aikos-home/roomkey/docs/fit-check-speaker.png

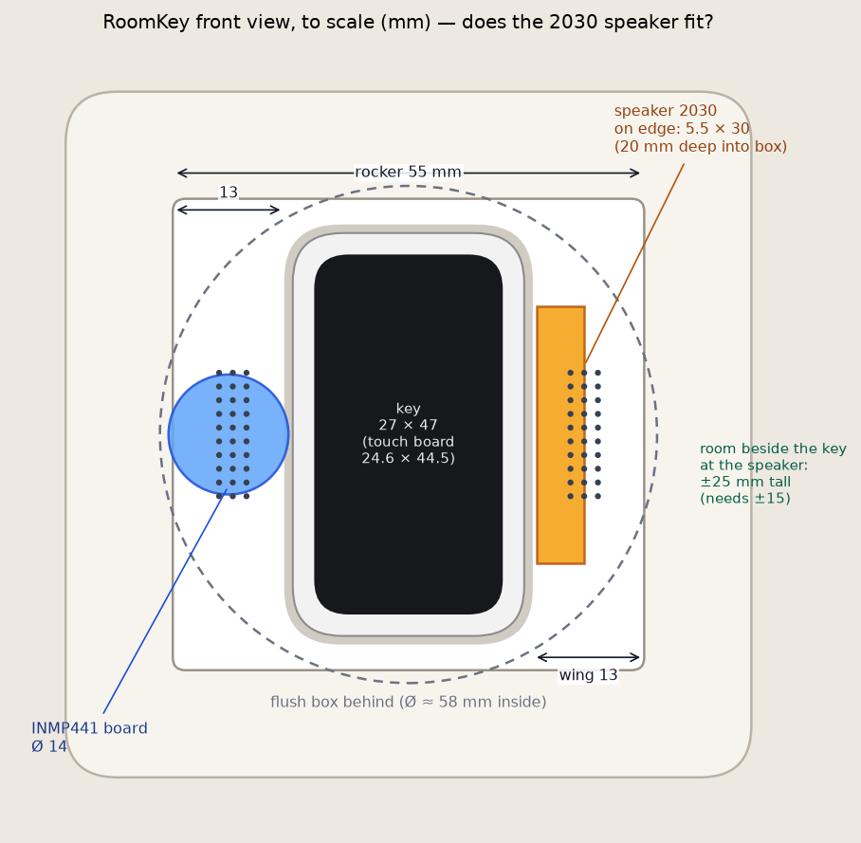
docs/fit-check-speaker.png
