aikos-home/roomkey/docs/north-star-v1.jpg

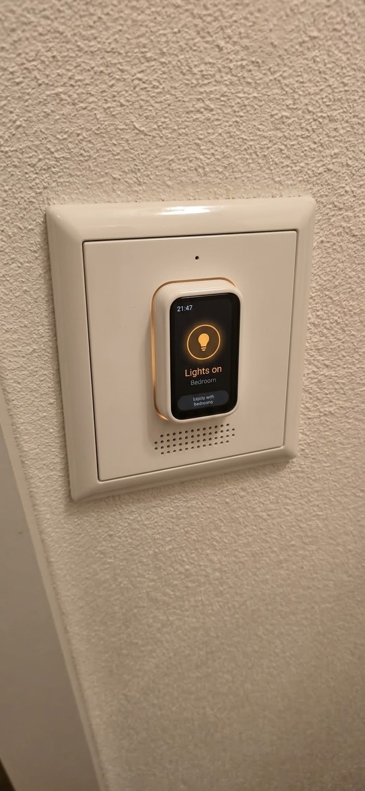
docs/north-star-v1.jpg
