aikos-home/roomkey/docs/screens/01_home_lights_off.png

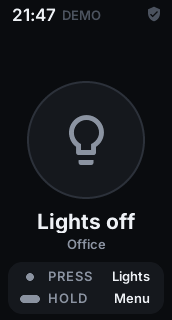
docs/screens/01_home_lights_off.png
