aikos-home/roomkey/docs/screens/02_home_hold_for_menu.png

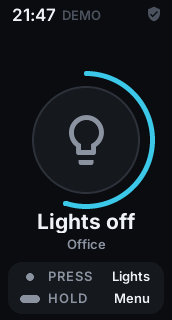
docs/screens/02_home_hold_for_menu.png
