aikos-home/roomkey/docs/screens/03_menu.png

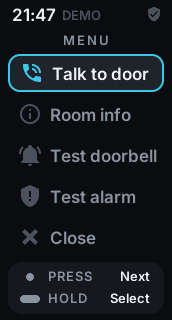
docs/screens/03_menu.png
