aikos-home/roomkey/docs/screens/05_doorbell_ringing.png

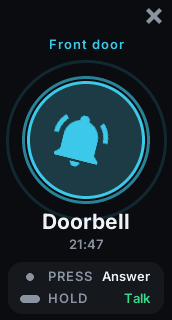
docs/screens/05_doorbell_ringing.png
