aikos-home/roomkey/docs/screens/06_call_talking_hold.png

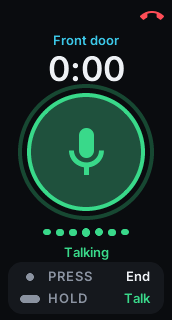
docs/screens/06_call_talking_hold.png
