aikos-home/roomkey/docs/screens/07_call_listening.png

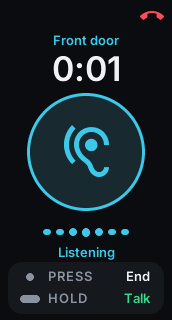
docs/screens/07_call_listening.png
