aikos-home/roomkey/docs/screens/09_home_armed_night.png

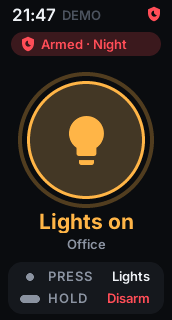
docs/screens/09_home_armed_night.png
