aikos-home/roomkey/docs/screens/10_home_hold_to_disarm.png

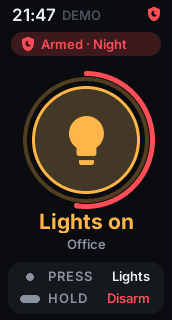
docs/screens/10_home_hold_to_disarm.png
