aikos-home/roomkey/docs/screens/11_disarming.png

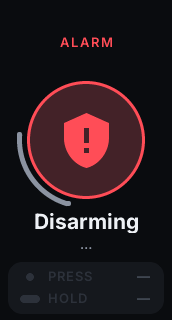
docs/screens/11_disarming.png
