aikos-home/roomkey/docs/screens/12_disarmed_flash.png

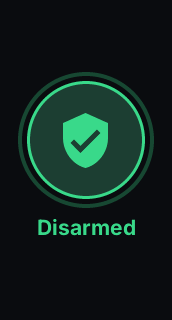
docs/screens/12_disarmed_flash.png
