aikos-home/roomkey/docs/screens/13_alarm_entry_delay.png

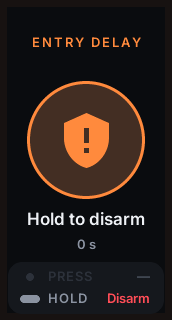
docs/screens/13_alarm_entry_delay.png
