aikos-home/roomkey/docs/screens/14_alarm_triggered.png

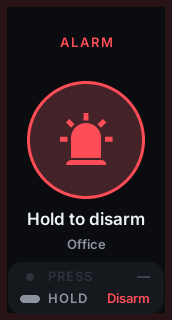
docs/screens/14_alarm_triggered.png
