aikos-home/roomkey/docs/screens/15_room_info.png

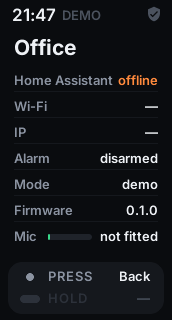
docs/screens/15_room_info.png
