aikos-home/roomkey/docs/screens/16_offline_toast.png

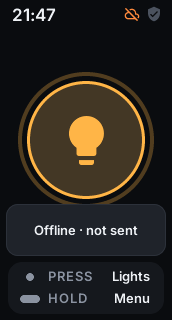
docs/screens/16_offline_toast.png
