aikos-home/roomkey/docs/screens/e2e_01_lights_on_via_ha.png

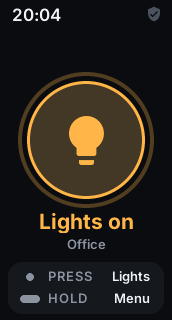
docs/screens/e2e_01_lights_on_via_ha.png
