aikos-home/roomkey/docs/screens/e2e_03_ring_from_ha_entity.png

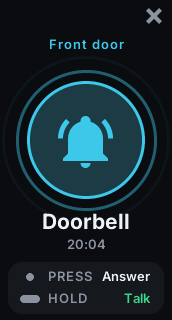
docs/screens/e2e_03_ring_from_ha_entity.png
