aikos-home/roomkey/docs/screens/e2e_04_entry_delay_from_ha.png

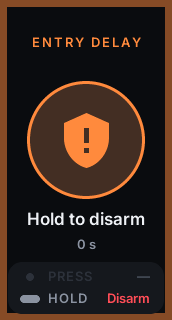
docs/screens/e2e_04_entry_delay_from_ha.png
