aikos-home/roomkey/hardware/drawings/insert-L_layers.png

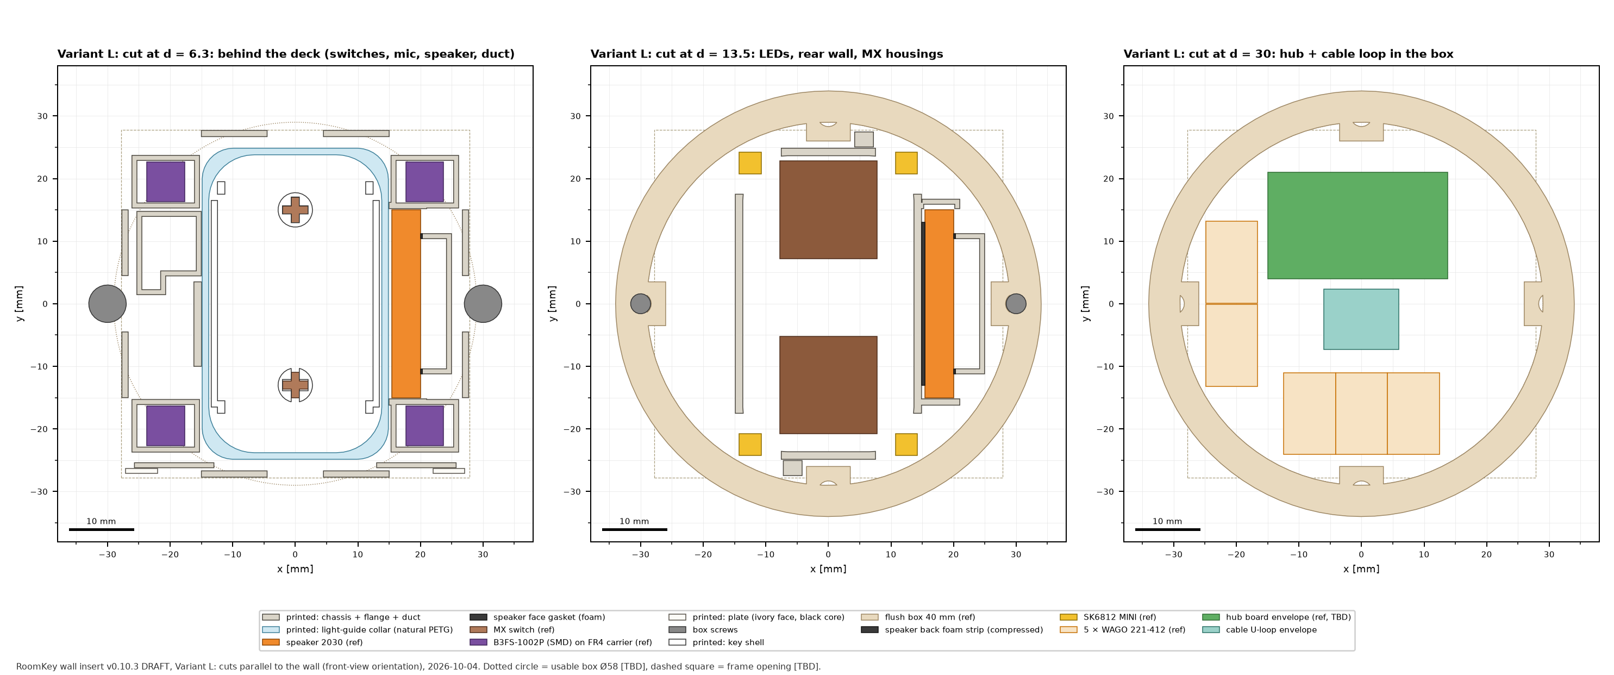
hardware/drawings/insert-L_layers.png
