aikos-home/roomkey/hardware/models/kit_chassis_3_rear_print.stl

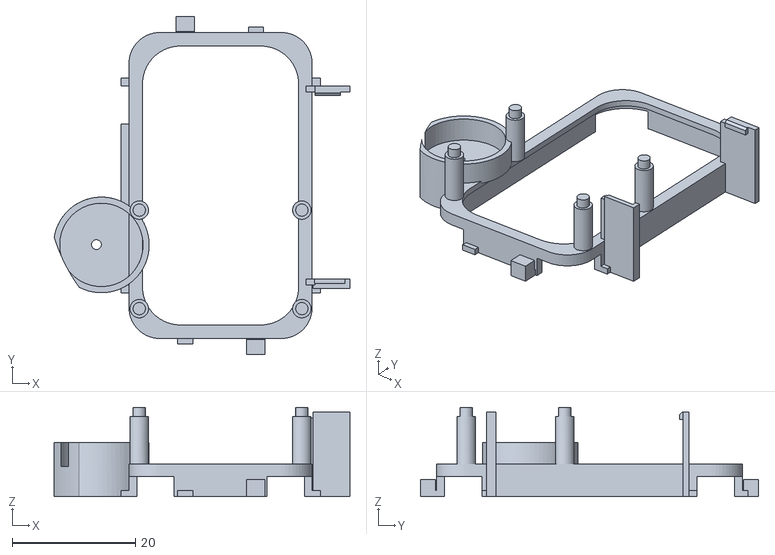
[picture p46: CAD file, 2026-10-08]
hardware/models/kit_chassis_3_rear_print.stl
48.0 x 54.9 x 14.5
