aikos-home/roomkey/hardware/models/chassis_S_2_flange.step

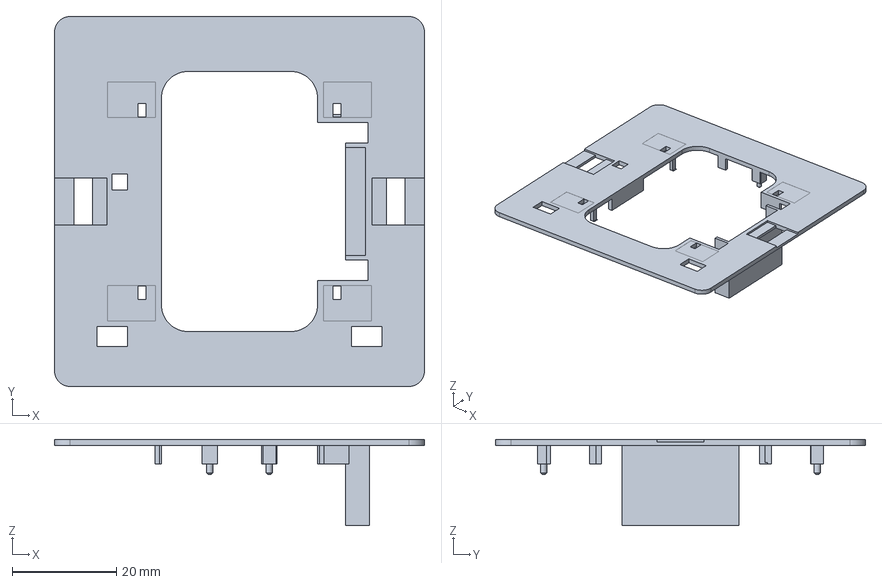
[picture p47: CAD file, 2026-10-08]
hardware/models/chassis_S_2_flange.step
71.0 x 71.0 x 16.5 mm
