aikos-home/roomkey/hardware/models/kit_chassis_2_flange.step

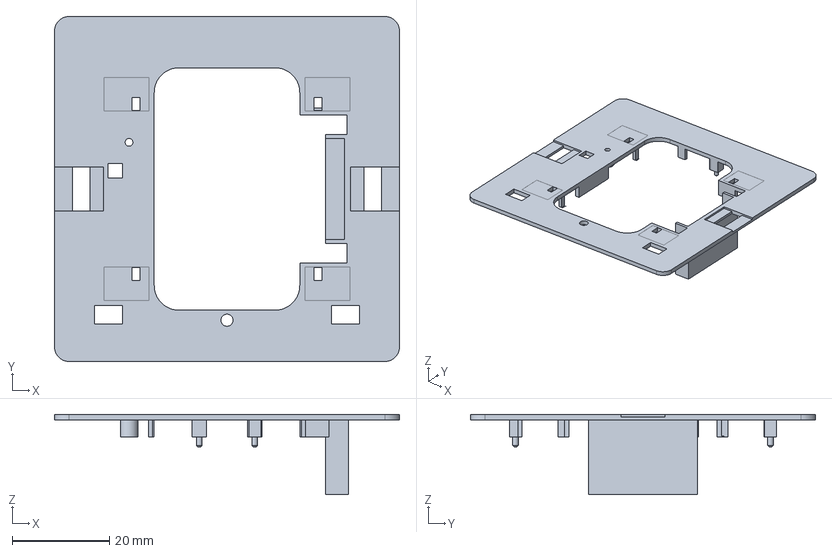
[picture p48: CAD file, 2026-10-08]
hardware/models/kit_chassis_2_flange.step
71.0 x 71.0 x 16.5 mm
