aikos-home/roomkey/hardware/models/chassis_L.step

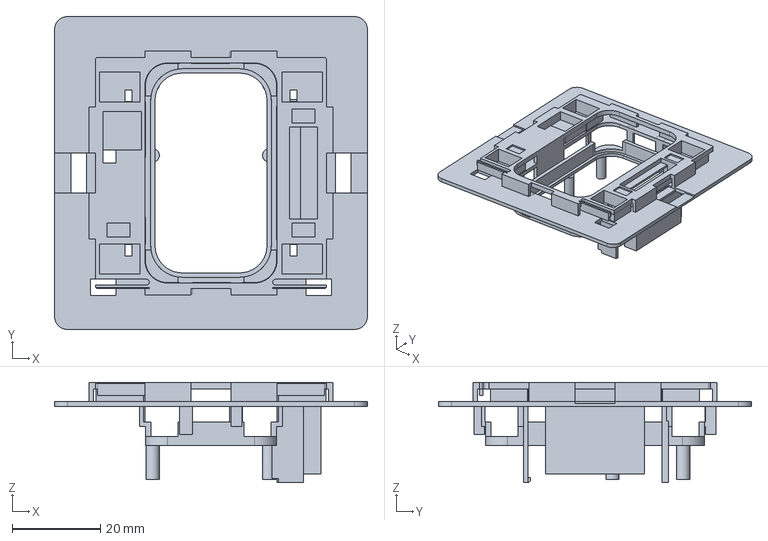
[picture p49: CAD file, 2026-10-08]
hardware/models/chassis_L.step
71.0 x 71.0 x 22.7 mm
