aikos-home/roomkey/hardware/models/switch_plate_print.stl

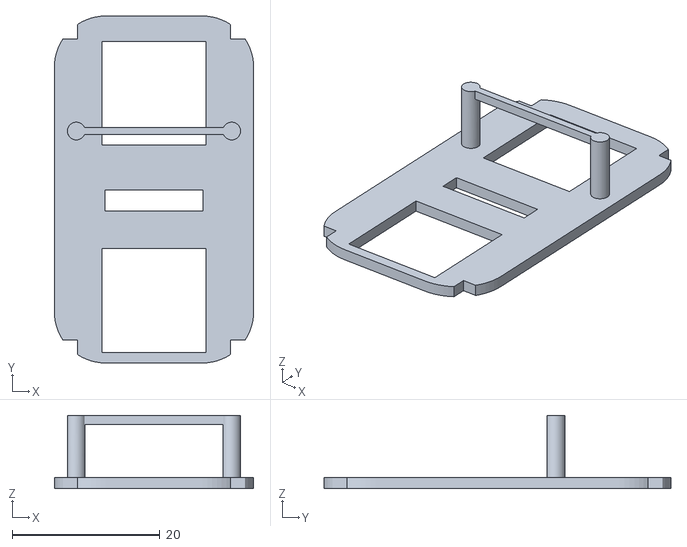
[picture p50: CAD file, 2026-10-08]
hardware/models/switch_plate_print.stl
27.0 x 46.9 x 9.90
