aikos-home/roomkey/hardware/models/kit-v0.10.3_ansicht.FCStd

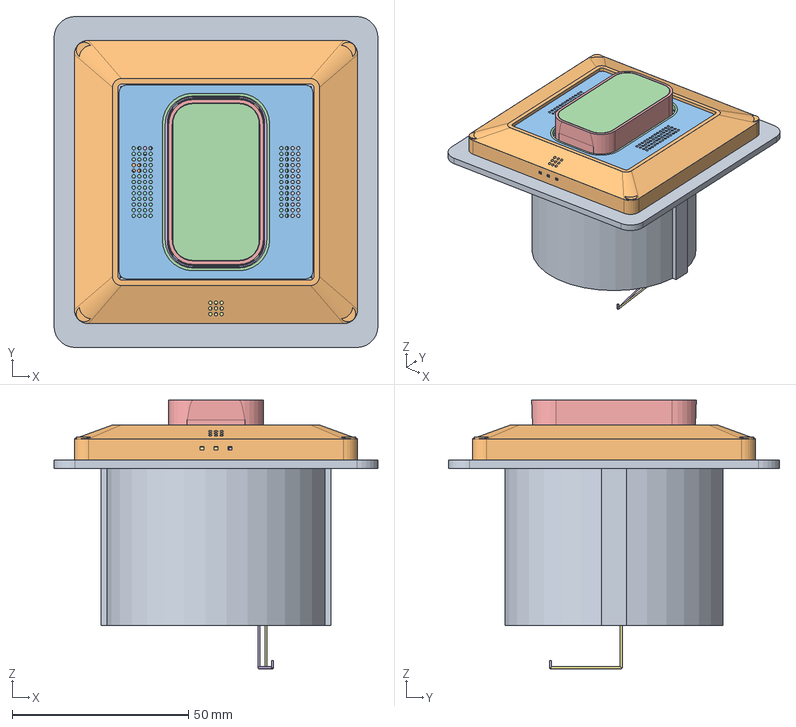
[picture p51: CAD file, 2026-10-08]
hardware/models/kit-v0.10.3_ansicht.FCStd
92.0 x 94.0 x 76.3 mm
Uebungsdose
Rahmen_JungAS500
Platte
Platte_Leuchtrand
Tastenschale_starr
Leuchtring
Schalterplatte
Chassis_1_vorne
Chassis_2_Flansch
Chassis_3_hinten
Technik_Traeger
Touch_Board
MX_oben
MX_unten
Lautsprecher
Radar_LD2410C
Radar_Stiftleiste
Radar_Chip_vorne
Radar_Randbauteile_vorne
Radar_Stiftstummel_vorne
Verstaerker_MAX98357A
Mikrofon_INMP441
Feuchtesensor_SHT31D_im_Rahmen
Kabelbogen_Taste
LED_1
LED_2
LED_3
LED_4
Schraube_links
Schraube_rechts
Draht 01 · 5 V → board · rot
Draht 02 · GND → board · schwarz
Draht 03 · KEY1 (Taste oben) · weiß
Draht 04 · KEY2 (Taste unten) · grau
Draht 05 · GND Taste oben · schwarz
Draht 06 · GND Taste unten (Brücke) · schwarz
Draht 07 · Radar TX → ESP RX · gelb
Draht 08 · ESP TX → Radar RX · grün
Draht 09 · 5 V Radar · rot
Draht 10 · GND Radar · schwarz
Draht 11 · I²S BCLK (Verstärker) · blau
Draht 12 · I²S WS (Verstärker) · violett
Draht 13 · I²S Daten → Verstärker · braun
Draht 14 · 5 V Verstärker · rot
Draht 15 · GND Verstärker · schwarz
Draht 16 · Lautsprecher + · rot
Draht 17 · Lautsprecher − · schwarz
Draht 18 · I²S BCLK (Mikrofon, vom Verstärker weiter) · blau
Draht 19 · I²S WS (Mikrofon, vom Verstärker weiter) · violett
Draht 20 · I²S Daten ← Mikrofon · rosa
Draht 21 · 3,3 V Mikrofon · orange
Draht 22 · L/R auf GND (linker Kanal) · schwarz
Draht 23 · GND Mikrofon · schwarz
Draht 24 · Labornetzteil +5,0 V · rot
Draht 25 · Labornetzteil GND · schwarz
Draht 26 · LED-Daten → LED unten rechts · gelb-grün
Draht 27 · LED-Daten → oben rechts · gelb-grün
Draht 28 · LED-Daten → oben links · gelb-grün
Draht 29 · LED-Daten → unten links · gelb-grün
Draht 30 · 5 V LED unten rechts · rot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
