aikos-home/roomkey/hardware/models/kit_chassis_1_front_print.stl

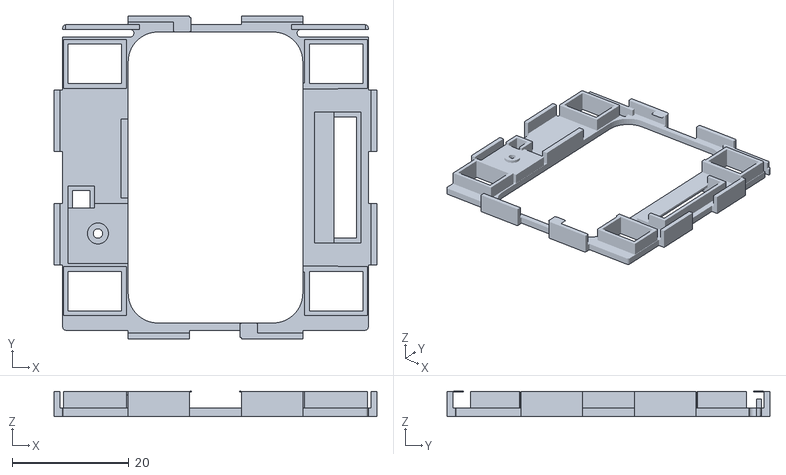
[picture p52: CAD file, 2026-10-08]
hardware/models/kit_chassis_1_front_print.stl
55.4 x 55.4 x 4.30
