aikos-home/roomkey/hardware/models/practice_frame_1x.step

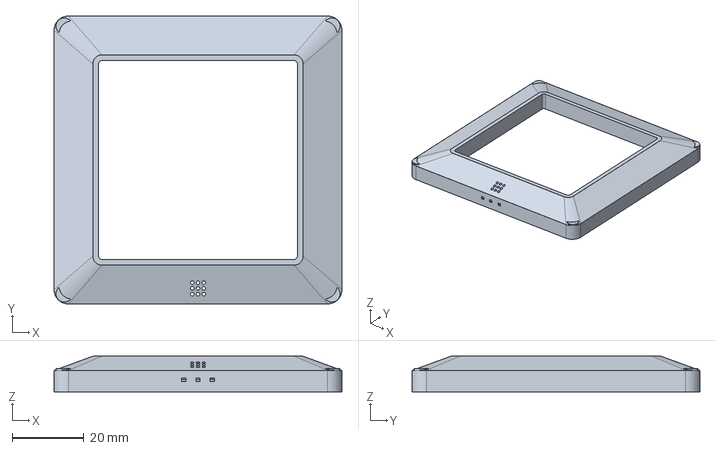
[picture p53: CAD file, 2026-10-06]
hardware/models/practice_frame_1x.step
80.5 x 80.5 x 10.0 mm
