aikos-home/roomkey/hardware/models/plate_L.step

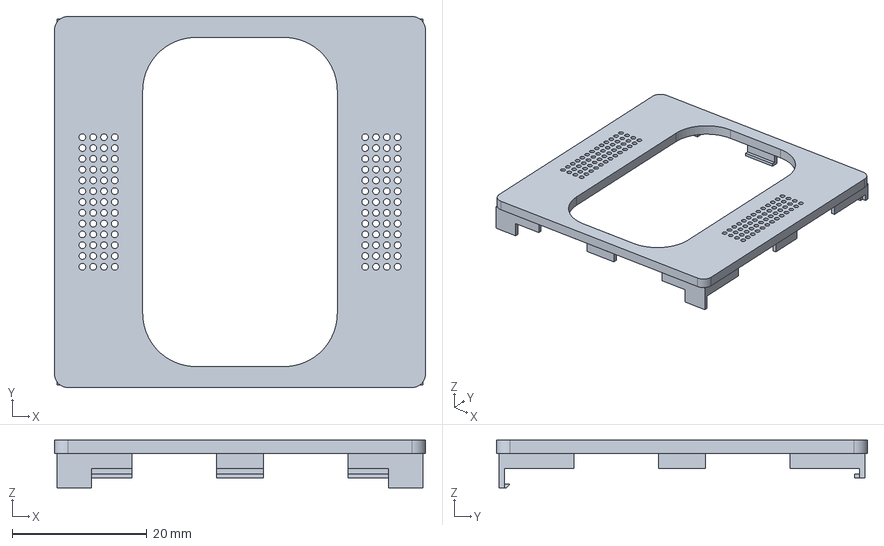
[picture p54: CAD file, 2026-10-04]
hardware/models/plate_L.step
55.0 x 55.0 x 7.10 mm
