aikos-home/roomkey/hardware/models/insert-L_wall-reference.step

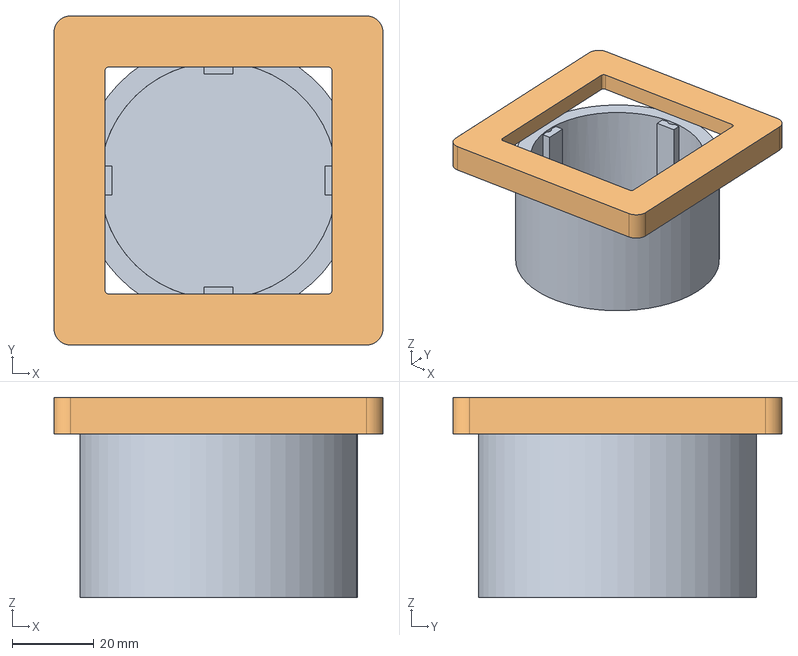
[picture p55: CAD file, 2026-10-04]
hardware/models/insert-L_wall-reference.step
80.5 x 80.5 x 49.0 mm
