aikos-home/roomkey/hardware/models/practice_box_print.stl

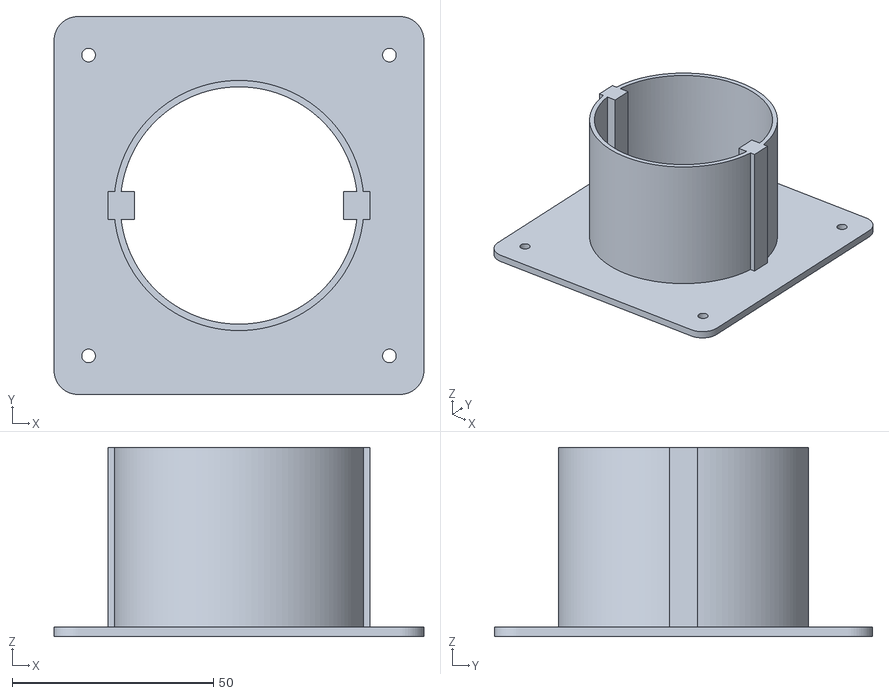
[picture p56: CAD file, 2026-10-04]
hardware/models/practice_box_print.stl
92.0 x 94.0 x 47.0
