aikos-home/roomkey/hardware/models/coupon-v1.step

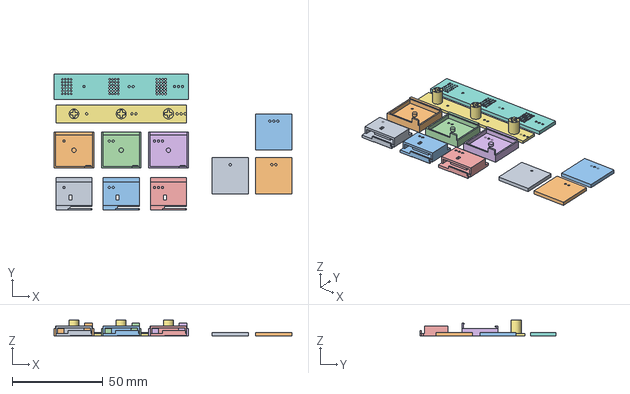
[picture p57: CAD file, 2026-10-01]
hardware/models/coupon-v1.step
131.0 x 75.0 x 8.80 mm
