aikos-home/roomkey/hardware/models/plate_S_body_print.stl

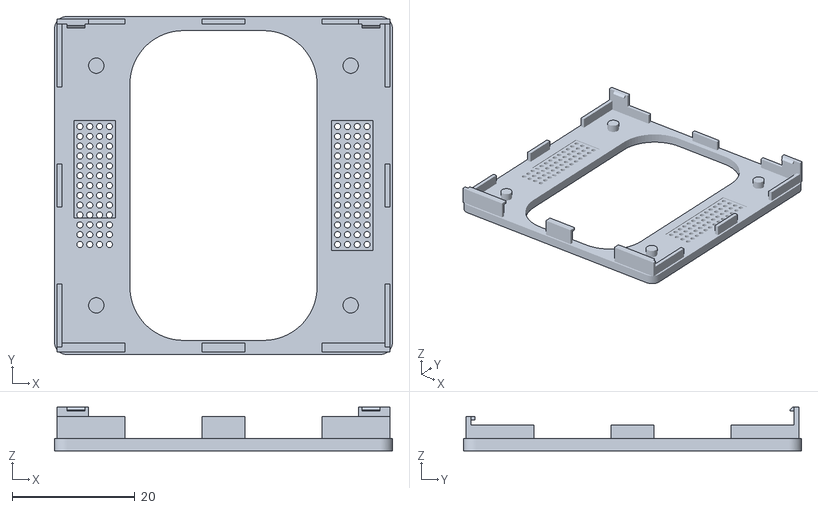
[picture p58: CAD file, 2026-10-01]
hardware/models/plate_S_body_print.stl
55.0 x 55.0 x 7.10
