aikos-home/roomkey/hardware/models/plate_L_glowrim_print.stl

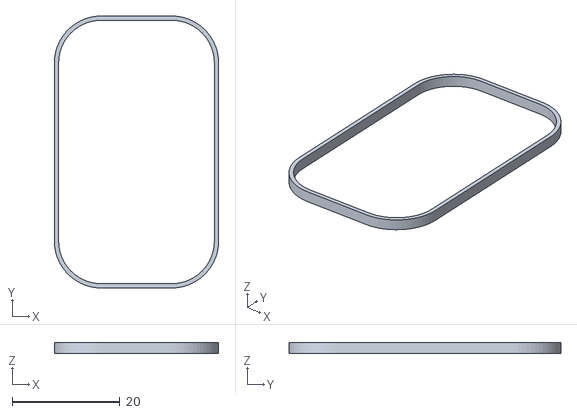
[picture p59: CAD file, 2026-10-01]
hardware/models/plate_L_glowrim_print.stl
30.5 x 50.4 x 2.00
