aikos-home/roomkey/esphome/src/roomkey_audio.h

#pragma once
// ─────────────────────────────────────────────────────────────────────────────
// RoomKey audio link (WIP) — half-duplex intercom media over UDP.
//
//   Format   RTP (RFC 3550) · L16 big-endian (RFC 3551) · 16 kHz · mono ·
//            dynamic payload type 96 · 20 ms / 320 samples per packet
//   Port     local UDP 5004 (configurable)
//   Peer     set explicitly (action set_intercom_peer) or *latched*: the first
//            host that streams to us becomes the peer (symmetric RTP) — so the
//            door station only needs to know the key's IP.
//
//   Tap      optional second destination (the local transcriber): every packet we SEND
//            also goes there, so what the room says can be transcribed. Only our own
//            microphone, only while we transmit (push-to-talk). Unset = off.
//
// Signalling (who talks when) is NOT here: it goes through Home Assistant
// (events answer / talk_start / talk_stop / hangup, action call_state).
// Threading: push_*() is called from the microphone task and only writes a
// lock-free SPSC ring; loop() runs in the main loop and owns the socket.
// ─────────────────────────────────────────────────────────────────────────────

#include <atomic>
#include <cmath>
#include <cstdint>
#include <cstdlib>
#include <cstring>
#include <functional>
#include <string>

#include "esphome/core/hal.h"
#include "roomkey_dsp.h"
#include "esphome/core/log.h"

#ifdef USE_HOST
#include <arpa/inet.h>
#include <fcntl.h>
#include <netdb.h>
#include <netinet/in.h>
#include <sys/socket.h>
#include <unistd.h>
#else
#include "lwip/netdb.h"
#include "lwip/sockets.h"
#endif

namespace roomkey {

class AudioLink {
 public:
  static constexpr int RATE = 16000;
  static constexpr int FRAME = 320;  // 20 ms
  static constexpr uint8_t PT_L16 = 96;

  bool begin(uint16_t port) {
    if (sock_ >= 0) return true;
    sock_ = ::socket(AF_INET, SOCK_DGRAM, IPPROTO_UDP);
    if (sock_ < 0) { ESP_LOGE(TAG, "socket() failed"); return false; }
    sockaddr_in a{};
    a.sin_family = AF_INET;
    a.sin_port = htons(port);
    a.sin_addr.s_addr = htonl(INADDR_ANY);
    if (::bind(sock_, (sockaddr *) &a, sizeof(a)) < 0) {
      ESP_LOGE(TAG, "bind(%u) failed", port);
      ::close(sock_);
      sock_ = -1;
      return false;
    }
    int fl = ::fcntl(sock_, F_GETFL, 0);
    ::fcntl(sock_, F_SETFL, fl | O_NONBLOCK);
    ssrc_ = 0x524B0000u ^ (uint32_t) esphome::millis();  // "RK" + noise
    port_ = port;
    ESP_LOGI(TAG, "RTP/L16 16 kHz listening on UDP %u", port);
    return true;
  }

  static bool resolve(const std::string &host, uint16_t port, sockaddr_in &a) {
    a = sockaddr_in{};
    a.sin_family = AF_INET;
    a.sin_port = htons(port);
    if (::inet_aton(host.c_str(), &a.sin_addr) != 0) return true;
    addrinfo hints{}, *res = nullptr;
    hints.ai_family = AF_INET;
    hints.ai_socktype = SOCK_DGRAM;
    if (::getaddrinfo(host.c_str(), nullptr, &hints, &res) != 0 || res == nullptr) {
      ESP_LOGW(TAG, "cannot resolve %s", host.c_str());
      return false;
    }
    a.sin_addr = ((sockaddr_in *) res->ai_addr)->sin_addr;
    ::freeaddrinfo(res);
    return true;
  }

  void set_peer(const std::string &host, uint16_t port) {
    sockaddr_in a;
    if (!resolve(host, port, a)) return;
    peer_ = a;
    has_peer_ = true;
    latched_ = false;
    clear_after_drain_ = false;
    keepalive_();  // resolve the peer's MAC now, not with the first words
    ESP_LOGI(TAG, "peer set to %s:%u", ::inet_ntoa(a.sin_addr), port);
  }
  void clear_peer() {
    if (closing_) { clear_after_drain_ = true; return; }  // still sending the last buffered words
    has_peer_ = false;
    latched_ = false;
  }
  // "host:port" of the transcriber, "" = off.
  void set_tap(const std::string &hp) {
    has_tap_ = false;
    size_t p = hp.rfind(':');
    if (p == std::string::npos || p == 0) {
      if (!hp.empty()) ESP_LOGW(TAG, "transcriber address must be host:port");
      return;
    }
    if (resolve(hp.substr(0, p), (uint16_t) atoi(hp.c_str() + p + 1), tap_)) {
      has_tap_ = true;
      keepalive_();
      ESP_LOGI(TAG, "transcriber tap %s", hp.c_str());
    }
  }
  // End of a call: forget a latched peer so the next caller can latch.
  void end_session() {
    set_tx(false);
    if (latched_) clear_peer();
  }
  // Accept incoming audio only while a call is active. Outside a call every packet is
  // dropped unheard and nobody can latch — otherwise any device on the LAN could play
  // sound in a bedroom.
  void set_accept(bool on) {
    if (accept_ && !on && latched_) clear_peer();
    accept_ = on;
  }
  // Where received audio goes (the speaker). Unset = received audio is only metered.
  std::function<void(const int16_t *, size_t)> sink;

  // Transmit gate (push-to-talk). On: a fresh start (stale samples are dropped). Off: take no
  // new samples, but still send what is buffered (≤ 256 ms), so the last word is not cut off.
  // to_peer = false: only the transcriber tap gets it (the test recording after a ring must never reach
  // the door; room audio goes to the door only while the key is held).
  void set_tx(bool on, bool to_peer = true) {
    if (on) {
      tail_.store(head_.load(std::memory_order_acquire));  // consumer-side drop of stale samples
      closing_ = false;
      to_peer_ = to_peer;
      tx_ = true;
    } else if (tx_) {
      closing_ = true;
    }
  }
  bool tx() const { return tx_ && !closing_; }

  // End-of-speech detection for timed recordings (mic task, once per mic block): speech is
  // VOICE_DB above the room's noise floor = the quietest block of the last ~1.5 s (speech has
  // gaps between words; steady noise does not). Muted start-up blocks don't count.
  void note_level(float db) { mic_gate.note(db, esphome::millis()); }
  float noise_floor_db() const { return mic_gate.floor_db(); }
  // Has anyone spoken since t0 (millis)?
  bool voiced_since(uint32_t t0) const { return mic_gate.voiced_since(t0); }
  uint32_t quiet_ms() const { return mic_gate.quiet_ms(esphome::millis()); }
  VoiceGate mic_gate;   // this key's mic (mic task)
  VoiceGate rx_gate;    // what comes in from the door (main loop): speech, not packets, ends a call (R17.8)

  // Producer side (microphone task): Q31 samples, optional gain.
  void push_q31(const int32_t *s, size_t n, float gain = 4.0f) {
    if (!tx_ || closing_) return;
    for (size_t i = 0; i < n; i++) {
      float v = (s[i] >> 16) * gain;
      put_((int16_t) (v > 32767.f ? 32767 : v < -32768.f ? -32768 : v));
    }
  }
  void push_s16(const int16_t *s, size_t n) {
    if (!tx_ || closing_) return;
    for (size_t i = 0; i < n; i++) put_(s[i]);
  }

  // Main loop: send complete frames, receive packets into `sink`.
  void loop() {
    if (sock_ < 0) return;
    // lwIP forgets a MAC address after 300 s without traffic and then drops all but 3 packets
    // while it asks again (measured: the first 220–300 ms of speech lost). A tiny RTP packet
    // every 60 s keeps peer and transcriber known. Receivers ignore packets without payload.
    if (!tx_ && (has_peer_ || has_tap_) && esphome::millis() - last_keepalive_ms_ > 60000) keepalive_();
    // Samples the mic task had to drop (ring full, main loop stalled): skip their sequence
    // numbers so the receiver sees a gap instead of silently spliced audio.
    uint32_t dropped = dropped_.exchange(0);
    if (dropped >= FRAME) {
      seq_ += dropped / FRAME;
      ts_ += (dropped / FRAME) * FRAME;
      overruns++;
    }
    // ── transmit ──
    while (tx_ && ((has_peer_ && to_peer_) || has_tap_) && avail_() >= FRAME) {
      uint8_t pkt[12 + FRAME * 2];
      pkt[0] = 0x80;
      pkt[1] = PT_L16 | (first_ ? 0x80 : 0);  // marker bit on the first packet of a talk spurt
      first_ = false;
      pkt[2] = seq_ >> 8; pkt[3] = seq_ & 0xFF;
      pkt[4] = ts_ >> 24; pkt[5] = ts_ >> 16; pkt[6] = ts_ >> 8; pkt[7] = ts_;
      pkt[8] = ssrc_ >> 24; pkt[9] = ssrc_ >> 16; pkt[10] = ssrc_ >> 8; pkt[11] = ssrc_;
      for (int i = 0; i < FRAME; i++) {
        int16_t v = get_();
        pkt[12 + 2 * i] = (uint16_t) v >> 8;  // L16 is network byte order
        pkt[13 + 2 * i] = v & 0xFF;
      }
      last_tx_ms_ = esphome::millis();
      if (has_peer_ && to_peer_ && ::sendto(sock_, pkt, sizeof(pkt), 0, (sockaddr *) &peer_, sizeof(peer_)) < 0) tx_err++;
      if (has_tap_ && !(has_peer_ && to_peer_ && same_(tap_, peer_)) &&   // the test recorder may BE the transcriber
          ::sendto(sock_, pkt, sizeof(pkt), 0, (sockaddr *) &tap_, sizeof(tap_)) < 0)
        tx_err++;
      seq_++;
      ts_ += FRAME;
      tx_pkts++;
    }
    if (closing_ && (avail_() < FRAME || !((has_peer_ && to_peer_) || has_tap_))) {  // buffer sent: now really off
      end_of_speech_();
      tx_ = closing_ = false;
      if (clear_after_drain_) has_peer_ = latched_ = clear_after_drain_ = false;
    }
    if (!tx_) first_ = true;
    // ── receive ──
    for (int guard = 0; guard < 16; guard++) {
      uint8_t buf[1500];
      sockaddr_in from{};
      socklen_t fl = sizeof(from);
      int n = ::recvfrom(sock_, buf, sizeof(buf), 0, (sockaddr *) &from, &fl);
      if (n <= 12) break;
      if (!accept_) { rx_dropped++; continue; }                        // no call → drop unheard
      if ((buf[0] >> 6) != 2 || (buf[1] & 0x7F) != PT_L16) continue;  // RTP v2, L16 only
      int hdr = 12 + 4 * (buf[0] & 0x0F);
      if (n <= hdr) continue;
      if (!has_peer_) {  // symmetric RTP: answer whoever talks to us
        peer_ = from;
        has_peer_ = latched_ = true;
        ESP_LOGI(TAG, "latched peer %s:%u", ::inet_ntoa(from.sin_addr), ntohs(from.sin_port));
      }
      size_t count = (n - hdr) / 2;
      int16_t pcm[(1500 - 12) / 2];
      float acc = 0;
      for (size_t i = 0; i < count; i++) {
        pcm[i] = (int16_t) ((buf[hdr + 2 * i] << 8) | buf[hdr + 2 * i + 1]);
        float f = pcm[i] / 32768.f;
        acc += f * f;
      }
      float db = 10.f * log10f(acc / (count ? count : 1) + 1e-12f);
      rx_gate.note(db, esphome::millis());
      float lvl = (db + 60.f) / 50.f;
      rx_level = lvl < 0 ? 0 : lvl > 1 ? 1 : lvl;
      rx_pkts++;
      last_rx_ms_ = esphome::millis();
      if (!tx_ && sink) sink(pcm, count);  // half-duplex: never play while talking
    }
    if (rx_level > 0 && esphome::millis() - last_rx_ms_ > 300) rx_level = 0;
  }

  bool active() const { return sock_ >= 0; }
  // A conversation starts: count its idle time from now, not from the last audio of an older one.
  void touch() { last_tx_ms_ = esphome::millis(); }
  // ms since audio last went out or came in (a call without audio for long ends by itself)
  uint32_t idle_ms() const {
    uint32_t last = last_tx_ms_ > last_rx_ms_ ? last_tx_ms_ : last_rx_ms_;
    return esphome::millis() - last;
  }
  uint32_t tx_pkts = 0, rx_pkts = 0, rx_dropped = 0, tx_err = 0, overruns = 0;
  float rx_level = 0;

 protected:
  static constexpr const char *TAG = "roomkey.audio";
  static constexpr uint32_t RING = 8192;  // 512 ms: survives a long LVGL redraw or Wi-Fi hiccup
  // RFC 3389 comfort noise (PT 13, 1-byte noise level): tells peer and transcriber "done talking",
  // so they don't have to wait for a timeout.
  void end_of_speech_() {
    uint8_t k[13] = {0x80, 13, (uint8_t) (seq_ >> 8), (uint8_t) seq_, (uint8_t) (ts_ >> 24), (uint8_t) (ts_ >> 16),
                     (uint8_t) (ts_ >> 8), (uint8_t) ts_, (uint8_t) (ssrc_ >> 24), (uint8_t) (ssrc_ >> 16),
                     (uint8_t) (ssrc_ >> 8), (uint8_t) ssrc_, 127};
    seq_++;
    if (has_peer_ && to_peer_) ::sendto(sock_, k, sizeof(k), 0, (sockaddr *) &peer_, sizeof(peer_));
    if (has_tap_ && !(has_peer_ && to_peer_ && same_(tap_, peer_))) ::sendto(sock_, k, sizeof(k), 0, (sockaddr *) &tap_, sizeof(tap_));
  }
  void keepalive_() {
    if (sock_ < 0) return;
    uint8_t k[12] = {0x80, PT_L16, (uint8_t) (seq_ >> 8), (uint8_t) seq_, 0, 0, 0, 0,
                     (uint8_t) (ssrc_ >> 24), (uint8_t) (ssrc_ >> 16), (uint8_t) (ssrc_ >> 8), (uint8_t) ssrc_};
    if (has_peer_) ::sendto(sock_, k, sizeof(k), 0, (sockaddr *) &peer_, sizeof(peer_));
    if (has_tap_) ::sendto(sock_, k, sizeof(k), 0, (sockaddr *) &tap_, sizeof(tap_));
    last_keepalive_ms_ = esphome::millis();
  }
  static bool same_(const sockaddr_in &a, const sockaddr_in &b) {
    return a.sin_addr.s_addr == b.sin_addr.s_addr && a.sin_port == b.sin_port;
  }
  void put_(int16_t v) {
    uint32_t h = head_.load(std::memory_order_relaxed);
    if (h - tail_.load(std::memory_order_acquire) >= RING) {  // full: drop, and tell loop() (seq gap)
      dropped_.fetch_add(1, std::memory_order_relaxed);
      return;
    }
    ring_[h % RING] = v;
    head_.store(h + 1, std::memory_order_release);
  }
  int16_t get_() {
    uint32_t t = tail_.load(std::memory_order_relaxed);
    int16_t v = ring_[t % RING];
    tail_.store(t + 1, std::memory_order_release);
    return v;
  }
  uint32_t avail_() const { return head_.load(std::memory_order_acquire) - tail_.load(std::memory_order_relaxed); }

  int sock_ = -1;
  uint16_t port_ = 0;
  sockaddr_in peer_{}, tap_{};
  bool has_tap_ = false;
  bool has_peer_ = false, latched_ = false, first_ = true, accept_ = false;
  volatile bool tx_ = false, closing_ = false, to_peer_ = true;
  uint32_t last_tx_ms_ = 0;
  bool clear_after_drain_ = false;
  uint16_t seq_ = 0;
  uint32_t ts_ = 0, ssrc_ = 0, last_rx_ms_ = 0;
  int16_t ring_[RING];
  std::atomic<uint32_t> head_{0}, tail_{0}, dropped_{0};
  uint32_t last_keepalive_ms_ = 0;
};

inline AudioLink &audio() {
  static AudioLink a;
  return a;
}

}  // namespace roomkey
